GOROman/calude-rom-cartridge/pcb/case/thing-3357677/images/2a6d291b604c4328ef77bd521af8f3c0.png

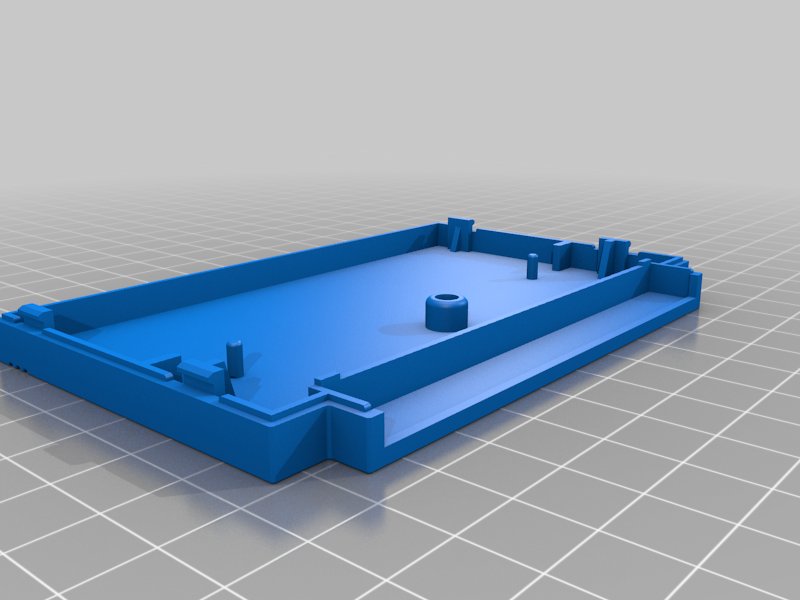
pcb/case/thing-3357677/images/2a6d291b604c4328ef77bd521af8f3c0.png
